MediaLabUniovi/GotchiLab_/docs/pinguino_construccion.png

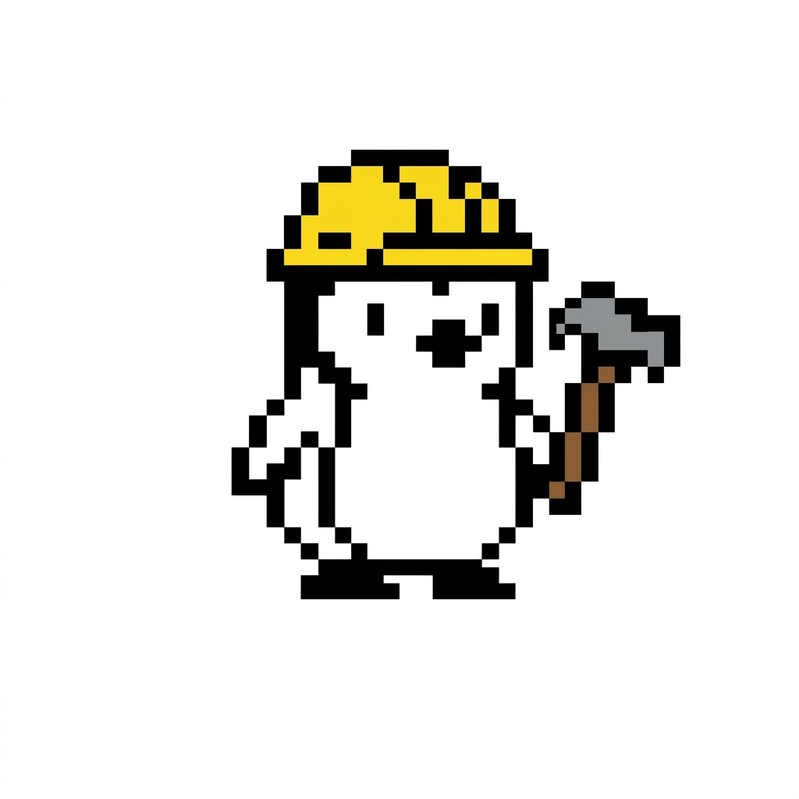
docs/pinguino_construccion.png
